Squirco/Sensor-Node-LS-V1/Firmware/squirco_LS_v0.5b/firmware_core/src/adc_lut.c

#include "adc_lut.h"

const uint16_t NTCTemp[] PROGMEM = //actual temperature in decimal * 10, represented in hex
{
	90,
	91,
	91,
	92,
	93,
	94,
	95,
	95,
	96,
	97,
	98,
	99,
	99,
	100,
	101,
	102,
	103,
	103,
	104,
	105,
	106,
	107,
	107,
	108,
	109,
	110,
	110,
	111,
	112,
	113,
	114,
	114,
	115,
	116,
	117,
	117,
	118,
	119,
	120,
	121,
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
};

const uint16_t ALSLux[][3] PROGMEM =
{
	{0 ,1, 0},
	{1 ,1, 1},
	{2 ,1, 5},
	{3 ,1, 9},
	{4 ,1, 11},
	{5 ,1, 13},
	{6 ,1, 15},
	{6 ,1, 16},
	{7 ,1, 17},
	{8 ,1, 18},
	{9 ,1, 19},
	{10 ,1, 20},
	{11 ,1, 21},
	{12 ,1, 22},
	{13 ,1, 22},
	{14 ,1, 23},
	{15 ,1, 23},
	{16 ,1, 24},
	{17 ,1, 24},
	{18 ,1, 25},
	{19 ,1, 25},
	{19 ,1, 26},
	{20 ,1, 26},
	{21 ,1, 27},
	{22 ,1, 27},
	{23 ,1, 27},
	{24 ,1, 28},
	{25 ,1, 28},
	{26 ,1, 28},
	{27 ,1, 29},
	{28 ,1, 29},
	{29 ,1, 29},
	{30 ,1, 29},
	{31 ,1, 30},
	{31 ,1, 30},
	{32 ,1, 30},
	{33 ,1, 30},
	{34 ,1, 31},
	{35 ,1, 31},
	{36 ,1, 31},
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
};
