Squirco/Sensor-Node-LS-V1/Firmware/squirco_LS_v0.5b/firmware_core/src/lwMesh/phy/at86rf212/src/phy.c

/**
 * \file phy.c
 *
 * \brief AT86RF212 PHY implementation
 *
 * Copyright (C) 2012-2014, Atmel Corporation. All rights reserved.
 *
 * \asf_license_start
 *
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
 * 3. The name of Atmel may not be used to endorse or promote products derived
 *    from this software without specific prior written permission.
 *
 * 4. This software may only be redistributed and used in connection with an
 *    Atmel microcontroller product.
 *
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
 * \asf_license_stop
 *
 * Modification and other use of this code is subject to Atmel's Limited
 * License Agreement (license.txt).
 *
 * $Id: phy.c 9267 2014-03-18 21:46:19Z ataradov $
 *
 */

#ifdef PHY_AT86RF212

/*- Includes ---------------------------------------------------------------*/
#include <stdbool.h>
#include "phy.h"
#include "halPhy.h"
#include "at86rf212.h"

/*- Definitions ------------------------------------------------------------*/
#define PHY_CRC_SIZE    2

/*- Types ------------------------------------------------------------------*/
typedef enum
{
  PHY_STATE_INITIAL,
  PHY_STATE_IDLE,
  PHY_STATE_SLEEP,
  PHY_STATE_TX_WAIT_END,
} PhyState_t;

/*- Prototypes -------------------------------------------------------------*/
static void phyWriteRegister(uint8_t reg, uint8_t value);
static uint8_t phyReadRegister(uint8_t reg);
static void phyWaitState(uint8_t state);
static void phyTrxSetState(uint8_t state);
static int8_t phyRssiBaseVal(void);
static void phySetChannel(void);
static void phySetRxState(void);

/*- Variables --------------------------------------------------------------*/
static PhyState_t phyState = PHY_STATE_INITIAL;
static uint8_t phyRxBuffer[128];
static bool phyRxState;
static uint8_t phyChannel;
static uint8_t phyBand;
static uint8_t phyModulation;

/*- Implementations --------------------------------------------------------*/

/*************************************************************************//**
*****************************************************************************/
void PHY_Init(void)
{
  HAL_PhyReset();

  phyRxState = false;
  phyBand = 0;
  phyModulation = phyReadRegister(TRX_CTRL_2_REG) & 0x3f;
  phyState = PHY_STATE_IDLE;

  phyWriteRegister(TRX_STATE_REG, TRX_CMD_TRX_OFF);
  phyWaitState(TRX_STATUS_TRX_OFF);

  phyWriteRegister(PHY_TX_PWR_REG, 0x41);

  phyWriteRegister(TRX_CTRL_1_REG, (1<<TX_AUTO_CRC_ON) | (3<<SPI_CMD_MODE) |
      (1<<IRQ_MASK_MODE));

  phyWriteRegister(TRX_CTRL_2_REG, (1<<RX_SAFE_MODE));
}

/*************************************************************************//**
*****************************************************************************/
void PHY_SetRxState(bool rx)
{
  phyRxState = rx;
  phySetRxState();
}

/*************************************************************************//**
*****************************************************************************/
void PHY_SetChannel(uint8_t channel)
{
  phyChannel = channel;
  phySetChannel();
}

/*************************************************************************//**
*****************************************************************************/
void PHY_SetBand(uint8_t band)
{
  phyBand = band;
  phySetChannel();
}

/*************************************************************************//**
*****************************************************************************/
void PHY_SetModulation(uint8_t modulation)
{
  phyModulation = modulation;
  phySetChannel();
}

/*************************************************************************//**
*****************************************************************************/
void PHY_SetPanId(uint16_t panId)
{
  uint8_t *d = (uint8_t *)&panId;

  phyWriteRegister(PAN_ID_0_REG, d[0]);
  phyWriteRegister(PAN_ID_1_REG, d[1]);
}

/*************************************************************************//**
*****************************************************************************/
void PHY_SetShortAddr(uint16_t addr)
{
  uint8_t *d = (uint8_t *)&addr;

  phyWriteRegister(SHORT_ADDR_0_REG, d[0]);
  phyWriteRegister(SHORT_ADDR_1_REG, d[1]);
  phyWriteRegister(CSMA_SEED_0_REG, d[0] + d[1]);
}

/*************************************************************************//**
*****************************************************************************/
void PHY_SetTxPower(uint8_t txPower)
{
  uint8_t reg;

  reg = phyReadRegister(PHY_TX_PWR_REG) & ~0x0f;
  phyWriteRegister(PHY_TX_PWR_REG, reg | txPower);
}

/*************************************************************************//**
*****************************************************************************/
void PHY_Sleep(void)
{
  phyTrxSetState(TRX_CMD_TRX_OFF);
  HAL_PhySlpTrSet();
  phyState = PHY_STATE_SLEEP;
}

/*************************************************************************//**
*****************************************************************************/
void PHY_Wakeup(void)
{
  HAL_PhySlpTrClear();
  phySetRxState();
  phyState = PHY_STATE_IDLE;
}

/*************************************************************************//**
*****************************************************************************/
void PHY_DataReq(uint8_t *data, uint8_t size)
{
  phyTrxSetState(TRX_CMD_TX_ARET_ON);

  phyReadRegister(IRQ_STATUS_REG);

  HAL_PhySpiSelect();
  HAL_PhySpiWriteByte(RF_CMD_FRAME_W);
  HAL_PhySpiWriteByte(size + PHY_CRC_SIZE);
  for (uint8_t i = 0; i < size; i++)
    HAL_PhySpiWriteByte(data[i]);
  HAL_PhySpiDeselect();

  phyState = PHY_STATE_TX_WAIT_END;
  HAL_PhySlpTrSet();
  HAL_PhySlpTrClear();
}

#ifdef PHY_ENABLE_RANDOM_NUMBER_GENERATOR
/*************************************************************************//**
*****************************************************************************/
uint16_t PHY_RandomReq(void)
{
  uint16_t rnd = 0;
  uint8_t rndValue;

  phyTrxSetState(TRX_CMD_RX_ON);

  for (uint8_t i = 0; i < 16; i += 2)
  {
    HAL_Delay(RANDOM_NUMBER_UPDATE_INTERVAL);
    rndValue = (phyReadRegister(PHY_RSSI_REG) >> RND_VALUE) & 3;
    rnd |= rndValue << i;
  }

  phySetRxState();

  return rnd;
}
#endif

#ifdef PHY_ENABLE_AES_MODULE
/*************************************************************************//**
*****************************************************************************/
void PHY_EncryptReq(uint8_t *text, uint8_t *key)
{
  HAL_PhySpiSelect();
  HAL_PhySpiWriteByte(RF_CMD_SRAM_W);
  HAL_PhySpiWriteByte(AES_CTRL_REG);
  HAL_PhySpiWriteByte((1<<AES_CTRL_MODE) | (0<<AES_CTRL_DIR));
  for (uint8_t i = 0; i < AES_BLOCK_SIZE; i++)
    HAL_PhySpiWriteByte(key[i]);
  HAL_PhySpiDeselect();

  HAL_PhySpiSelect();
  HAL_PhySpiWriteByte(RF_CMD_SRAM_W);
  HAL_PhySpiWriteByte(AES_CTRL_REG);
  HAL_PhySpiWriteByte((0<<AES_CTRL_MODE) | (0<<AES_CTRL_DIR));
  for (uint8_t i = 0; i < AES_BLOCK_SIZE; i++)
    HAL_PhySpiWriteByte(text[i]);
  HAL_PhySpiWriteByte((1<<AES_CTRL_REQUEST) | (0<<AES_CTRL_MODE) | (0<<AES_CTRL_DIR));
  HAL_PhySpiDeselect();

  HAL_Delay(AES_CORE_CYCLE_TIME);

  HAL_PhySpiSelect();
  HAL_PhySpiWriteByte(RF_CMD_SRAM_R);
  HAL_PhySpiWriteByte(AES_STATE_REG);
  for (uint8_t i = 0; i < AES_BLOCK_SIZE; i++)
    text[i] = HAL_PhySpiWriteByte(0);
  HAL_PhySpiDeselect();
}
#endif

#ifdef PHY_ENABLE_ENERGY_DETECTION
/*************************************************************************//**
*****************************************************************************/
int8_t PHY_EdReq(void)
{
  uint8_t ed;

  phyTrxSetState(TRX_CMD_RX_ON);
  phyWriteRegister(PHY_ED_LEVEL_REG, 0);

  while (0 == (phyReadRegister(IRQ_STATUS_REG) & (1<<CCA_ED_DONE)));

  ed = (int8_t)phyReadRegister(PHY_ED_LEVEL_REG);

  phySetRxState();

  return ed + phyRssiBaseVal();
}
#endif

/*************************************************************************//**
*****************************************************************************/
static void phyWriteRegister(uint8_t reg, uint8_t value)
{
  HAL_PhySpiSelect();
  HAL_PhySpiWriteByteInline(RF_CMD_REG_W | reg);
  HAL_PhySpiWriteByteInline(value);
  HAL_PhySpiDeselect();
}

/*************************************************************************//**
*****************************************************************************/
static uint8_t phyReadRegister(uint8_t reg)
{
  uint8_t value;

  HAL_PhySpiSelect();
  HAL_PhySpiWriteByteInline(RF_CMD_REG_R | reg);
  value = HAL_PhySpiWriteByteInline(0);
  HAL_PhySpiDeselect();

  return value;
}

/*************************************************************************//**
*****************************************************************************/
static void phyWaitState(uint8_t state)
{
  while (state != (phyReadRegister(TRX_STATUS_REG) & TRX_STATUS_MASK));
}

/*************************************************************************//**
*****************************************************************************/
static void phySetChannel(void)
{
  uint8_t reg;

  reg = phyReadRegister(TRX_CTRL_2_REG) & ~0x3f;
  phyWriteRegister(TRX_CTRL_2_REG, reg | phyModulation);

  phyWriteRegister(CC_CTRL_1_REG, phyBand);

  if (0 == phyBand)
  {
    reg = phyReadRegister(PHY_CC_CCA_REG) & ~0x1f;
    phyWriteRegister(PHY_CC_CCA_REG, reg | phyChannel);
  }
  else
  {
    phyWriteRegister(CC_CTRL_0_REG, phyChannel);
  }
}

/*************************************************************************//**
*****************************************************************************/
static void phySetRxState(void)
{
  phyTrxSetState(TRX_CMD_TRX_OFF);

  phyReadRegister(IRQ_STATUS_REG);

  if (phyRxState)
    phyTrxSetState(TRX_CMD_RX_AACK_ON);
}

/*************************************************************************//**
*****************************************************************************/
static void phyTrxSetState(uint8_t state)
{
  phyWriteRegister(TRX_STATE_REG, TRX_CMD_FORCE_TRX_OFF);
  phyWaitState(TRX_STATUS_TRX_OFF);

  phyWriteRegister(TRX_STATE_REG, state);
  phyWaitState(state);
}

/*************************************************************************//**
*****************************************************************************/
static int8_t phyRssiBaseVal(void)
{
  bool oqpsk = (phyModulation & (1<<BPSK_OQPSK));
  bool sub   = (phyModulation & (1<<SUB_MODE));
  bool rc    = (phyModulation & (1<<OQPSK_SUB1_RC_EN));

  if (0 == oqpsk)
  {
    if (0 == sub)
      return PHY_RSSI_BASE_VAL_BPSK_20;
    else
      return PHY_RSSI_BASE_VAL_BPSK_40;
  }
  else
  {
    if (0 == sub)
      return PHY_RSSI_BASE_VAL_OQPSK_SIN_RC_100;
    else
    {
      if (0 == rc)
        return PHY_RSSI_BASE_VAL_OQPSK_SIN_250;
      else
        return PHY_RSSI_BASE_VAL_OQPSK_RC_250;
    }
  }
}

/*************************************************************************//**
*****************************************************************************/
void PHY_TaskHandler(void)
{
  if (PHY_STATE_SLEEP == phyState)
    return;

  if (phyReadRegister(IRQ_STATUS_REG) & (1<<TRX_END))
  {
    if (PHY_STATE_IDLE == phyState)
    {
      PHY_DataInd_t ind;
      uint8_t size;
      int8_t rssi;

      rssi = (int8_t)phyReadRegister(PHY_ED_LEVEL_REG);

      HAL_PhySpiSelect();
      HAL_PhySpiWriteByte(RF_CMD_FRAME_R);
      size = HAL_PhySpiWriteByte(0);
      for (uint8_t i = 0; i < size + 1/*lqi*/; i++)
        phyRxBuffer[i] = HAL_PhySpiWriteByte(0);
      HAL_PhySpiDeselect();

      ind.data = phyRxBuffer;
      ind.size = size - PHY_CRC_SIZE;
      ind.lqi  = phyRxBuffer[size];
      ind.rssi = rssi + phyRssiBaseVal();
      PHY_DataInd(&ind);

      phyWaitState(TRX_STATUS_RX_AACK_ON);
    }

    else if (PHY_STATE_TX_WAIT_END == phyState)
    {
      uint8_t status = (phyReadRegister(TRX_STATE_REG) >> TRAC_STATUS) & 7;

      if (TRAC_STATUS_SUCCESS == status)
        status = PHY_STATUS_SUCCESS;
      else if (TRAC_STATUS_CHANNEL_ACCESS_FAILURE == status)
        status = PHY_STATUS_CHANNEL_ACCESS_FAILURE;
      else if (TRAC_STATUS_NO_ACK == status)
        status = PHY_STATUS_NO_ACK;
      else
        status = PHY_STATUS_ERROR;

      phySetRxState();
      phyState = PHY_STATE_IDLE;

      PHY_DataConf(status);
    }
  }
}

#endif // PHY_AT86RF212
