Squirco/Sensor-Node-LS-V1/Firmware/squirco_LS_v0.5b/firmware_core/src/lwMesh/hal/drivers/atmega1281/halUart.c

/**
 * \file halUart.c
 *
 * \brief ATmega1281 UART implementation
 *
 * Copyright (C) 2012-2014, Atmel Corporation. All rights reserved.
 *
 * \asf_license_start
 *
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
 * 3. The name of Atmel may not be used to endorse or promote products derived
 *    from this software without specific prior written permission.
 *
 * 4. This software may only be redistributed and used in connection with an
 *    Atmel microcontroller product.
 *
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
 * \asf_license_stop
 *
 * Modification and other use of this code is subject to Atmel's Limited
 * License Agreement (license.txt).
 *
 * $Id: halUart.c 9267 2014-03-18 21:46:19Z ataradov $
 *
 */

/*- Includes ---------------------------------------------------------------*/
#include <stdbool.h>
#include "hal.h"
#include "halUart.h"
#include "config.h"

/*- Definitions ------------------------------------------------------------*/
#ifndef HAL_UART_TX_FIFO_SIZE
#define HAL_UART_TX_FIFO_SIZE  10
#endif

#ifndef HAL_UART_RX_FIFO_SIZE
#define HAL_UART_RX_FIFO_SIZE  10
#endif

#ifndef HAL_UART_CHANNEL
#define HAL_UART_CHANNEL       0
#endif

#if HAL_UART_CHANNEL == 0
  #define UBRRxH            UBRR0H
  #define UBRRxL            UBRR0L
  #define UCSRxA            UCSR0A
  #define UCSRxB            UCSR0B
  #define UCSRxC            UCSR0C
  #define UDRx              UDR0
  #define USARTx_UDRE_vect  USART0_UDRE_vect
  #define USARTx_RX_vect    USART0_RX_vect
#elif HAL_UART_CHANNEL == 1
  #define UBRRxH            UBRR1H
  #define UBRRxL            UBRR1L
  #define UCSRxA            UCSR1A
  #define UCSRxB            UCSR1B
  #define UCSRxC            UCSR1C
  #define UDRx              UDR1
  #define USARTx_UDRE_vect  USART1_UDRE_vect
  #define USARTx_RX_vect    USART1_RX_vect
#else
  #error Unsupported UART channel
#endif

/*- Types ------------------------------------------------------------------*/
typedef struct
{
  uint16_t  head;
  uint16_t  tail;
  uint16_t  size;
  uint16_t  bytes;
  uint8_t   *data;
} FifoBuffer_t;

/*- Variables --------------------------------------------------------------*/
static FifoBuffer_t txFifo;
static uint8_t txData[HAL_UART_TX_FIFO_SIZE+1];

static volatile FifoBuffer_t rxFifo;
static uint8_t rxData[HAL_UART_RX_FIFO_SIZE+1];

static volatile bool udrEmpty;
static volatile bool newData;

/*- Implementations --------------------------------------------------------*/

/*************************************************************************//**
*****************************************************************************/
void HAL_UartInit(uint32_t baudrate)
{
  uint32_t brr = ((uint32_t)F_CPU * 2) / (16 * baudrate) - 1;

  UBRRxH = (brr >> 8) & 0xff;
  UBRRxL = (brr & 0xff);
  UCSRxA = (1 << U2X1);
  UCSRxB = (1 << TXEN1) | (1 << RXEN1) | (1 << RXCIE1);
  UCSRxC = (3 << UCSZ10);

  txFifo.data = txData;
  txFifo.size = HAL_UART_TX_FIFO_SIZE;
  txFifo.bytes = 0;
  txFifo.head = 0;
  txFifo.tail = 0;

  rxFifo.data = rxData;
  rxFifo.size = HAL_UART_RX_FIFO_SIZE;
  rxFifo.bytes = 0;
  rxFifo.head = 0;
  rxFifo.tail = 0;

  udrEmpty = true;
  newData = false;
}

/*************************************************************************//**
*****************************************************************************/
void HAL_UartWriteByte(uint8_t byte)
{
  if (txFifo.bytes == txFifo.size)
    return;

  txFifo.data[txFifo.tail++] = byte;
  if (txFifo.tail == txFifo.size)
    txFifo.tail = 0;
  txFifo.bytes++;
}

/*************************************************************************//**
*****************************************************************************/
uint8_t HAL_UartReadByte(void)
{
  uint8_t byte;

  PRAGMA(diag_suppress=Pa082);
  ATOMIC_SECTION_ENTER
    byte = rxFifo.data[rxFifo.head++];
    if (rxFifo.head == rxFifo.size)
      rxFifo.head = 0;
    rxFifo.bytes--;
  ATOMIC_SECTION_LEAVE
  PRAGMA(diag_default=Pa082);

  return byte;
}

/*************************************************************************//**
*****************************************************************************/
ISR(USARTx_UDRE_vect)
{
  udrEmpty = true;
  UCSRxB &= ~(1 << UDRIE1);
}

/*************************************************************************//**
*****************************************************************************/
ISR(USARTx_RX_vect)
{
  PRAGMA(diag_suppress=Pa082);

  uint8_t status = UCSRxA;
  uint8_t byte = UDRx;

  if (0 == (status & ((1 << FE1) | (1 << DOR1) | (1 << UPE1))))
  {
    if (rxFifo.bytes == rxFifo.size)
      return;

    rxFifo.data[rxFifo.tail++] = byte;
    if (rxFifo.tail == rxFifo.size)
      rxFifo.tail = 0;
    rxFifo.bytes++;

    newData = true;
  }

  PRAGMA(diag_default=Pa082);
}

/*************************************************************************//**
*****************************************************************************/
void HAL_UartTaskHandler(void)
{
  if (txFifo.bytes && udrEmpty)
  {
    uint8_t byte;

    byte = txFifo.data[txFifo.head++];
    if (txFifo.head == txFifo.size)
      txFifo.head = 0;
    txFifo.bytes--;

    ATOMIC_SECTION_ENTER
      UDRx = byte;
      UCSRxB |= (1 << UDRIE1);
      udrEmpty = false;
    ATOMIC_SECTION_LEAVE
  }

  {
    uint16_t bytes;
    bool new;

    ATOMIC_SECTION_ENTER
      new = newData;
      newData = false;
      bytes = rxFifo.bytes;
    ATOMIC_SECTION_LEAVE

    if (new)
      HAL_UartBytesReceived(bytes);
  }
}
